partofcosmos-site/pocket-companion/assets/cdn_audit/01_system_architecture_block_diagram.png

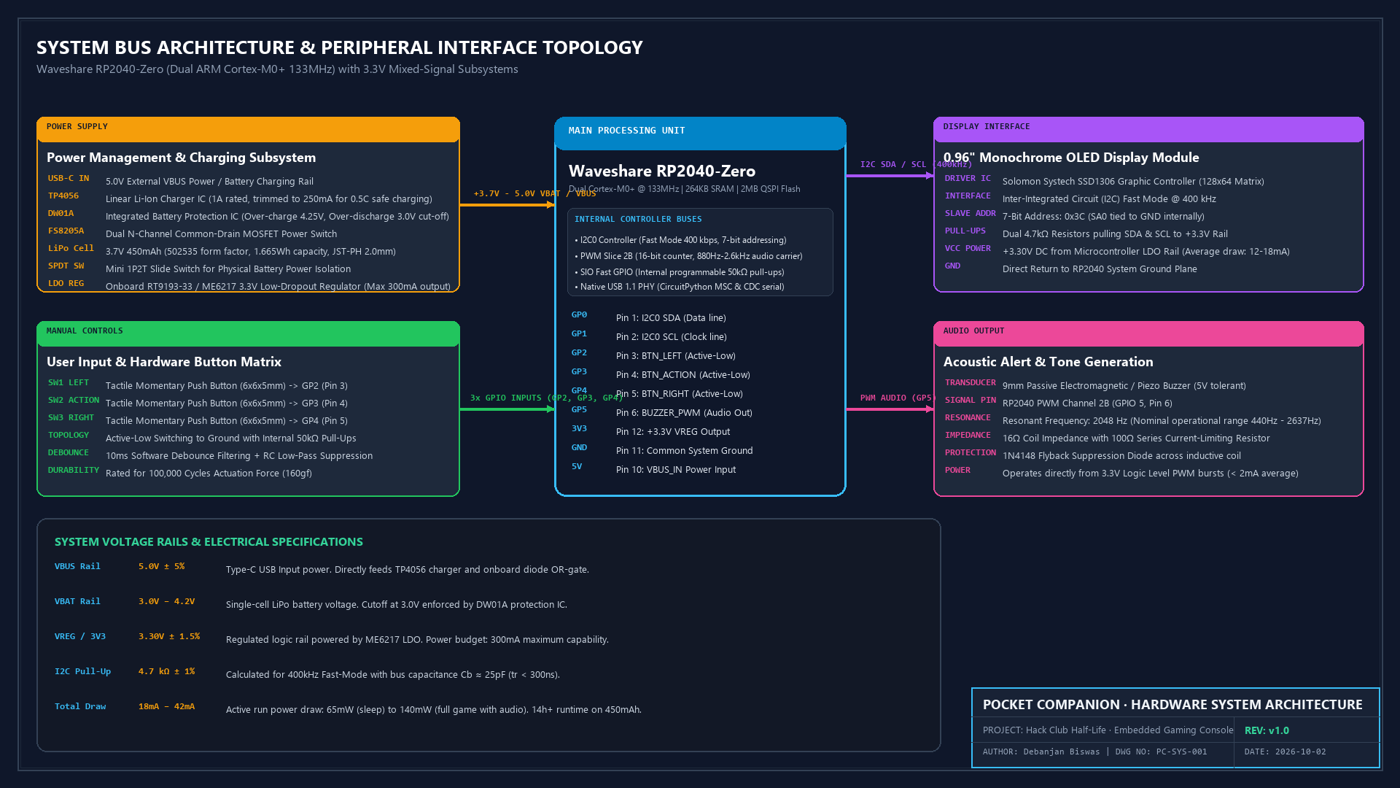
assets/cdn_audit/01_system_architecture_block_diagram.png
