partofcosmos-site/pocket-companion/assets/cdn_audit/02_rp2040_pinout_peripheral_matrix.png

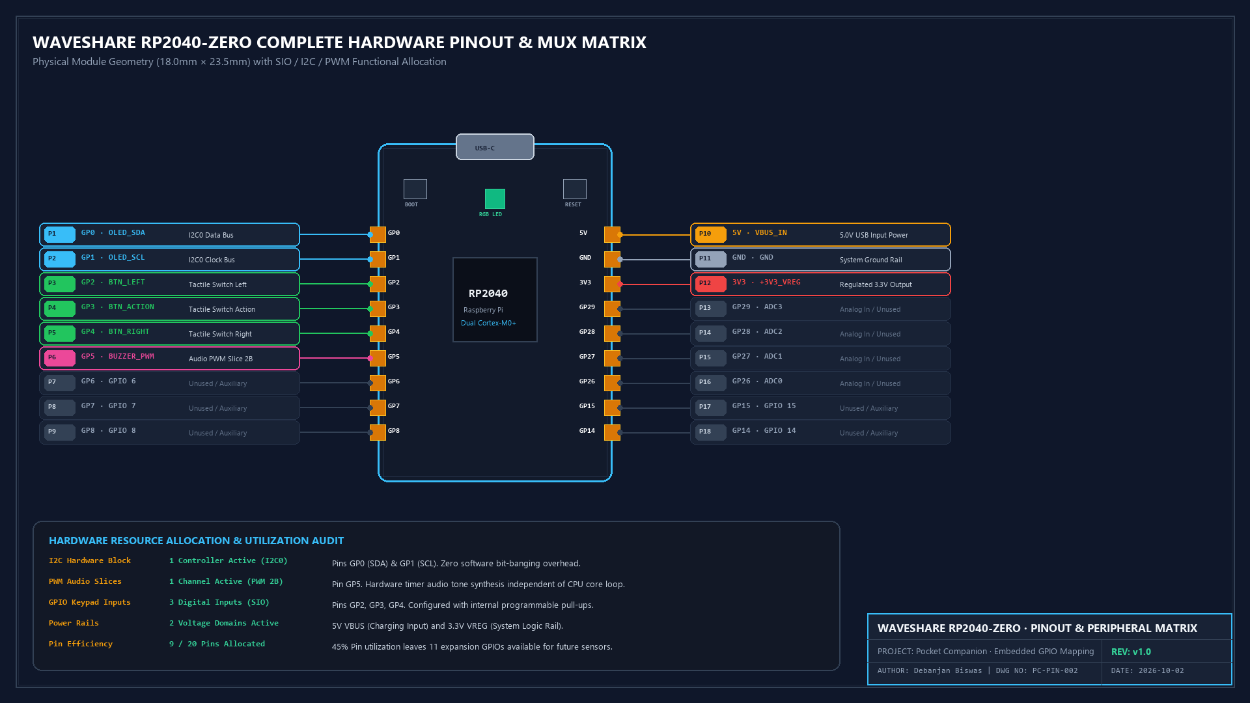
assets/cdn_audit/02_rp2040_pinout_peripheral_matrix.png
