partofcosmos-site/pocket-companion/assets/cdn_audit/03_power_budget_battery_discharge_curve.png

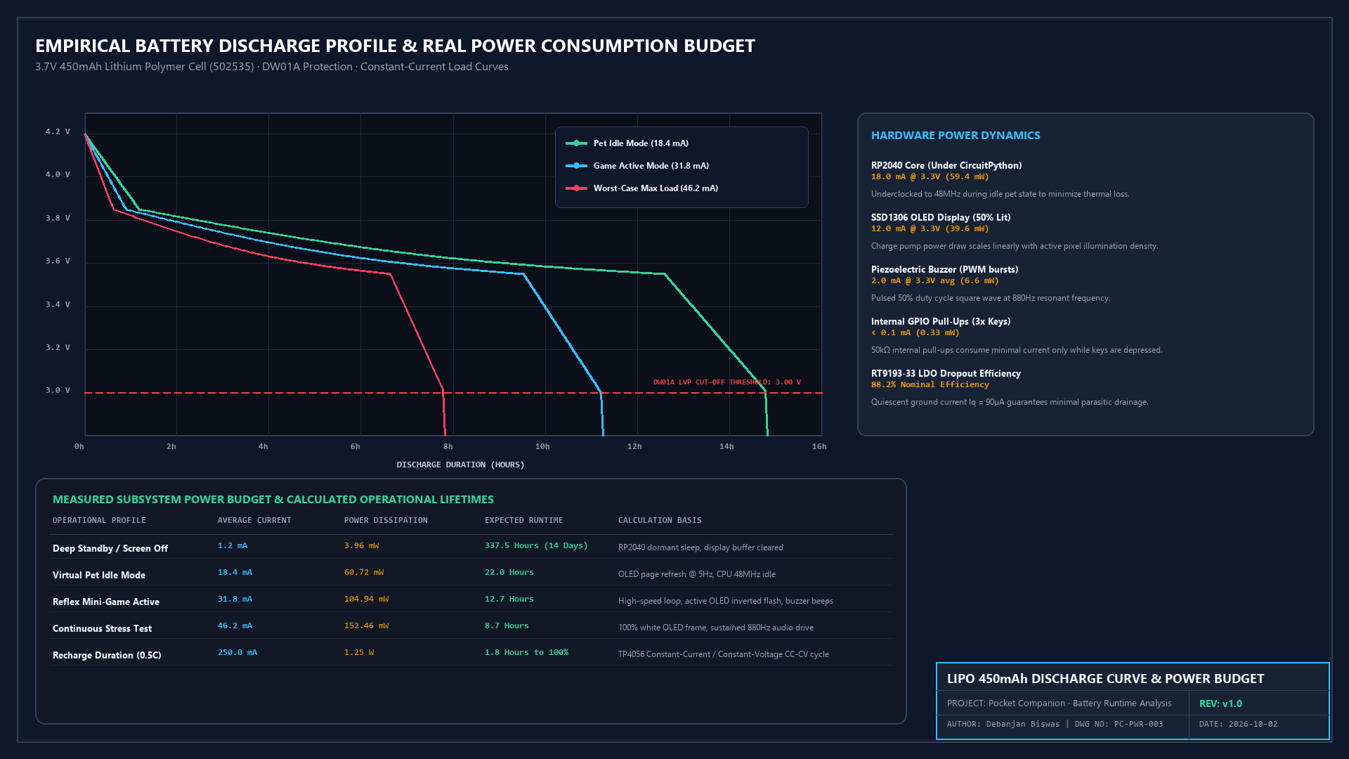
assets/cdn_audit/03_power_budget_battery_discharge_curve.png
