partofcosmos-site/pocket-companion/assets/cdn_audit/05_easyeda_schematic_capture.png

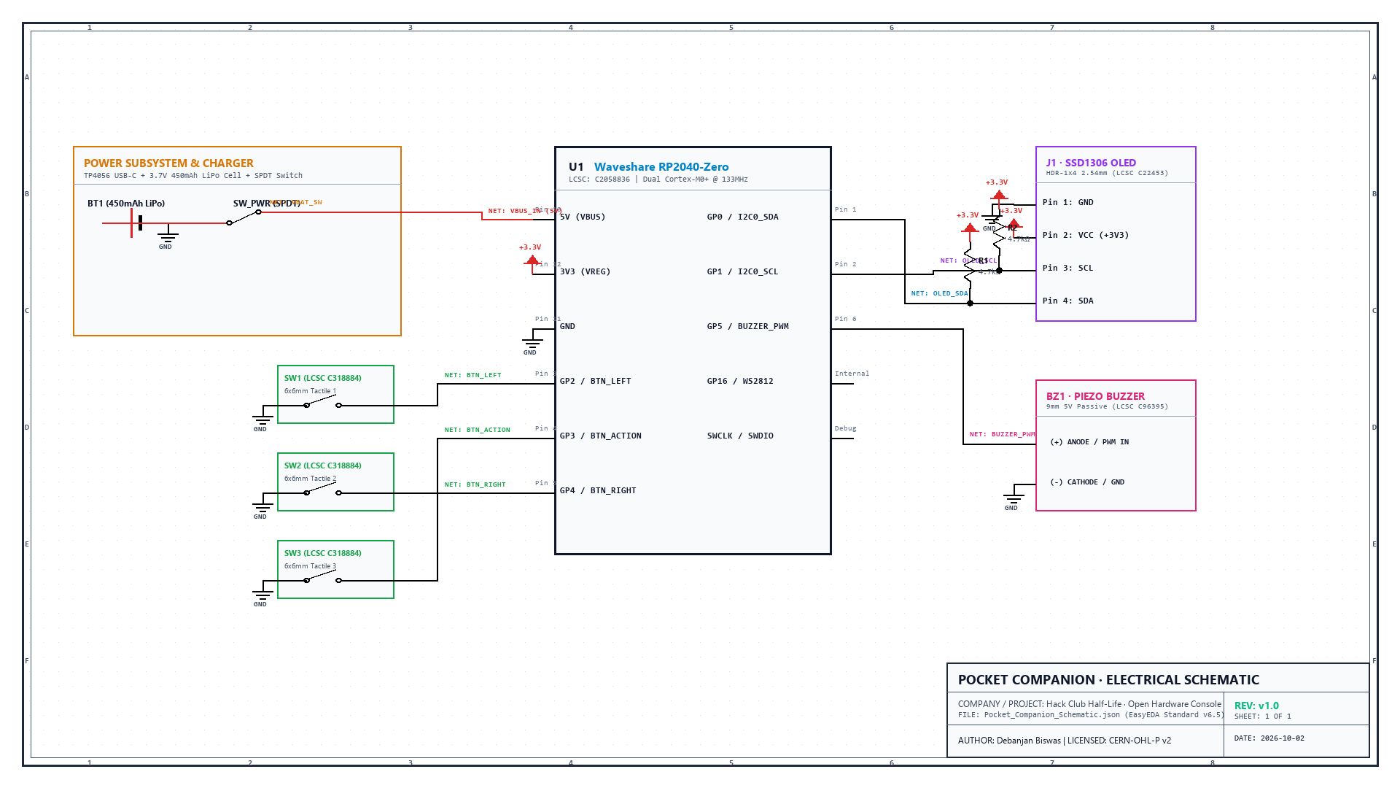
assets/cdn_audit/05_easyeda_schematic_capture.png
