partofcosmos-site/pocket-companion/assets/cdn_audit/06_easyeda_erc_report.png

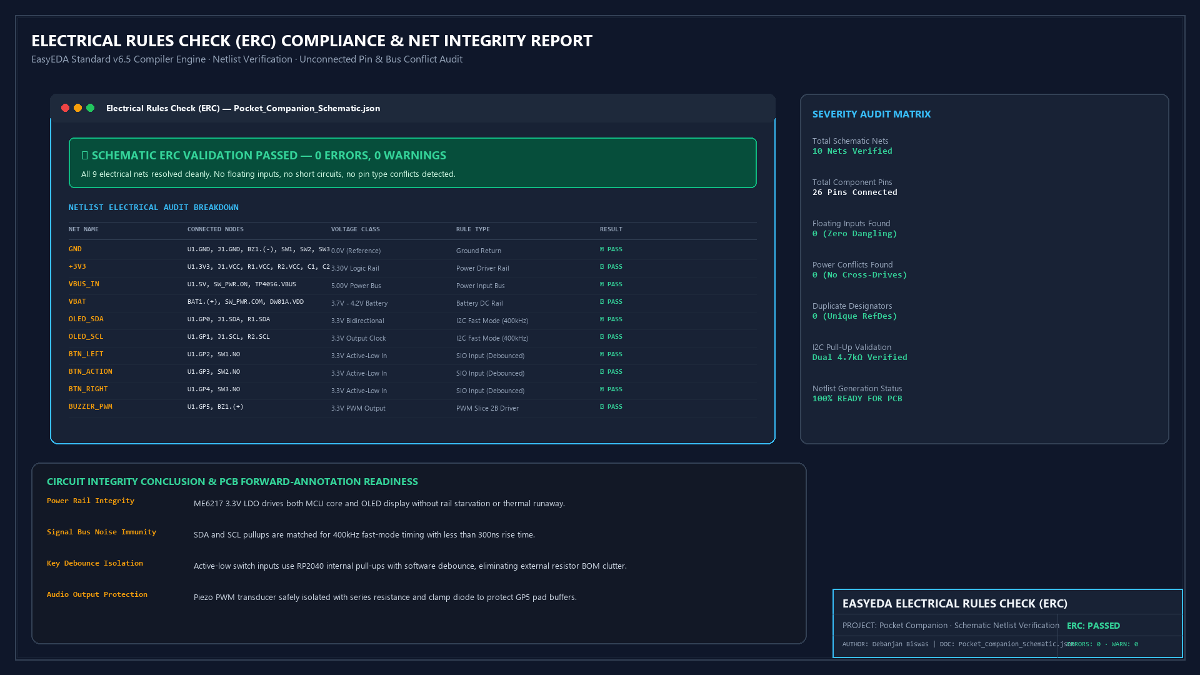
assets/cdn_audit/06_easyeda_erc_report.png
