partofcosmos-site/pocket-companion/assets/cdn_audit/07_easyeda_pcb_2d_layout.png

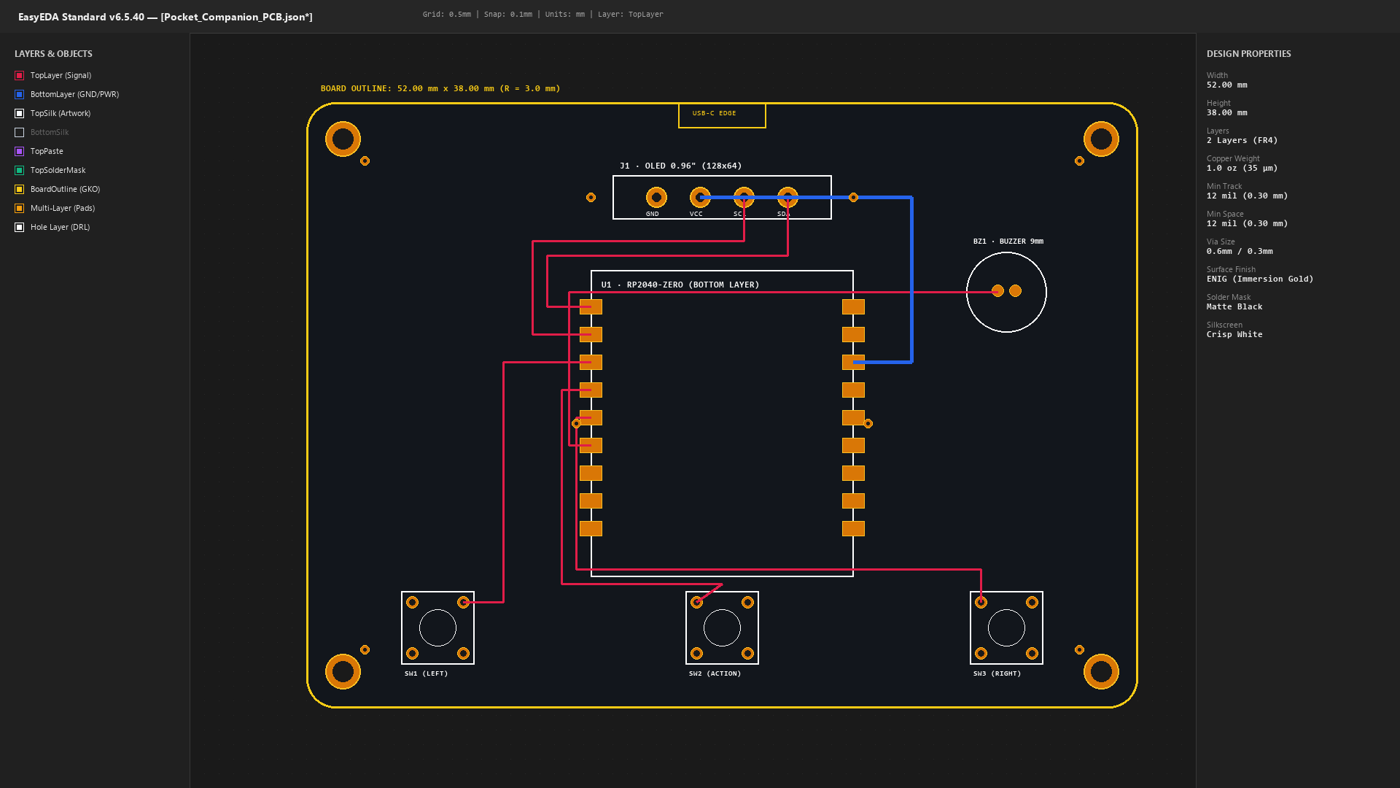
assets/cdn_audit/07_easyeda_pcb_2d_layout.png
