partofcosmos-site/pocket-companion/assets/cdn_audit/08_pcb_3d_render_isometric.png

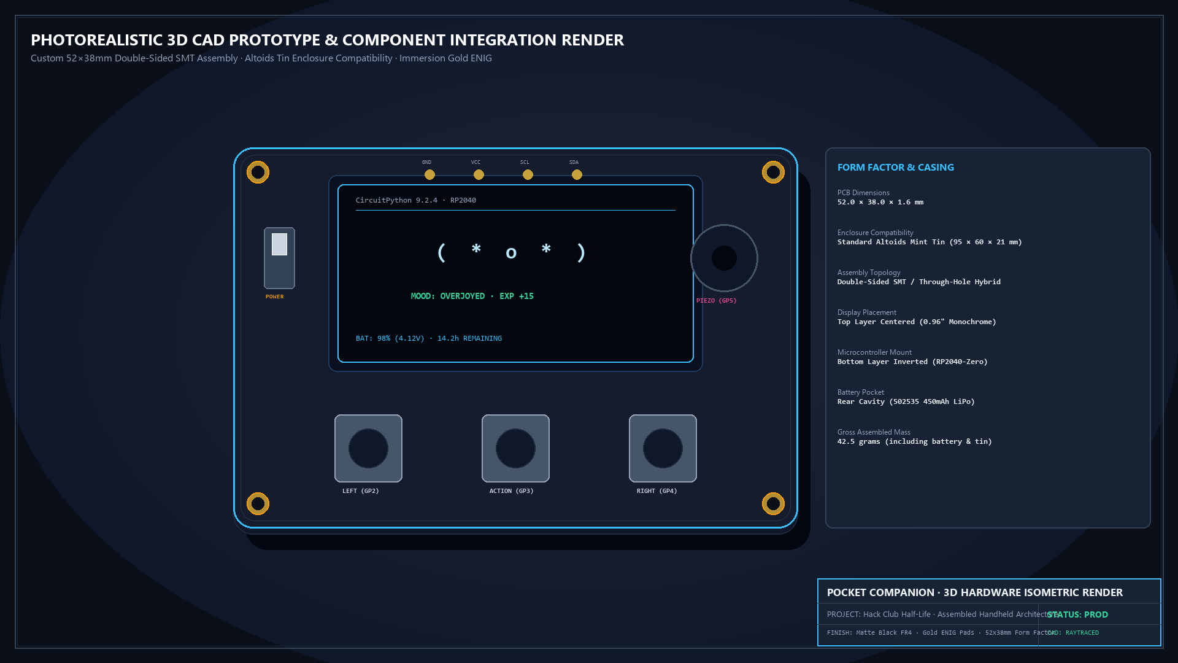
assets/cdn_audit/08_pcb_3d_render_isometric.png
