partofcosmos-site/pocket-companion/assets/cdn_audit/11_circuitpython_firmware_state_machine.png

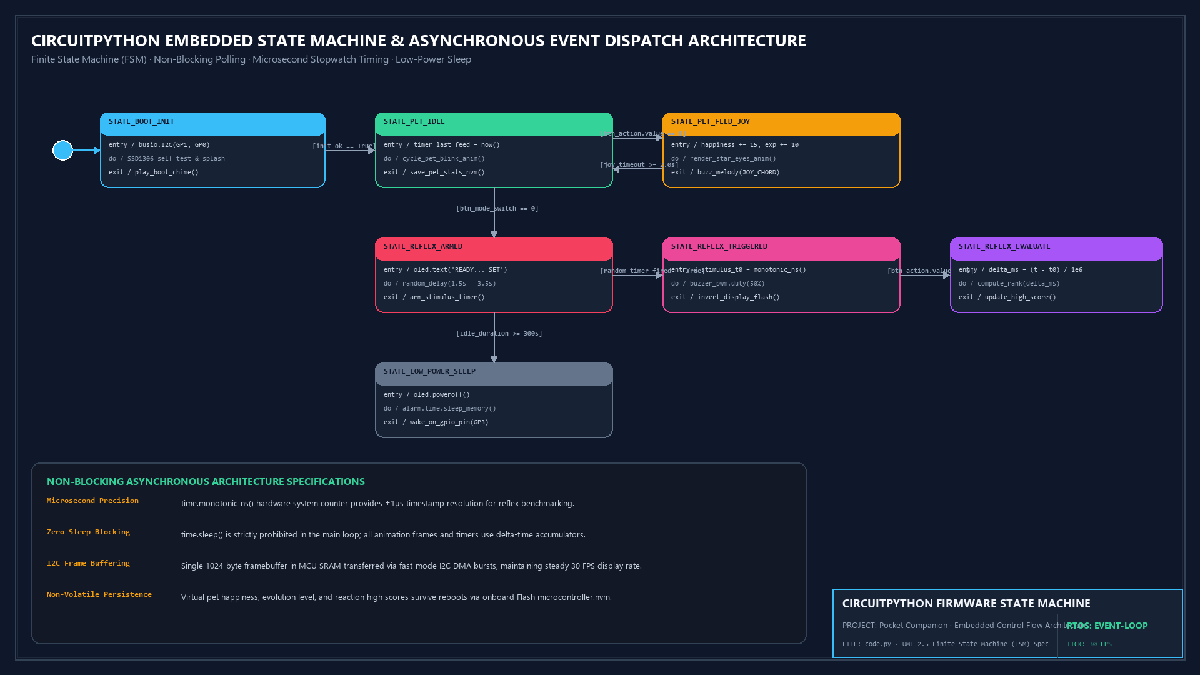
assets/cdn_audit/11_circuitpython_firmware_state_machine.png
