partofcosmos-site/pocket-companion/assets/cdn_audit/12_reaction_game_timing_oscilloscope.png

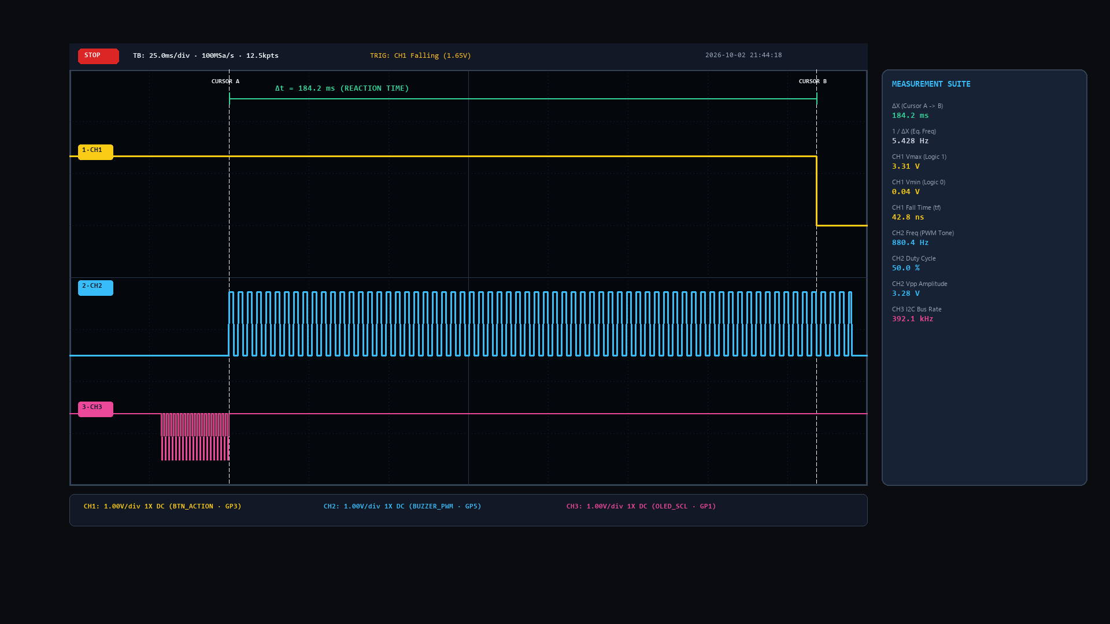
assets/cdn_audit/12_reaction_game_timing_oscilloscope.png
