partofcosmos-site/pocket-companion/assets/cutaway_section.png

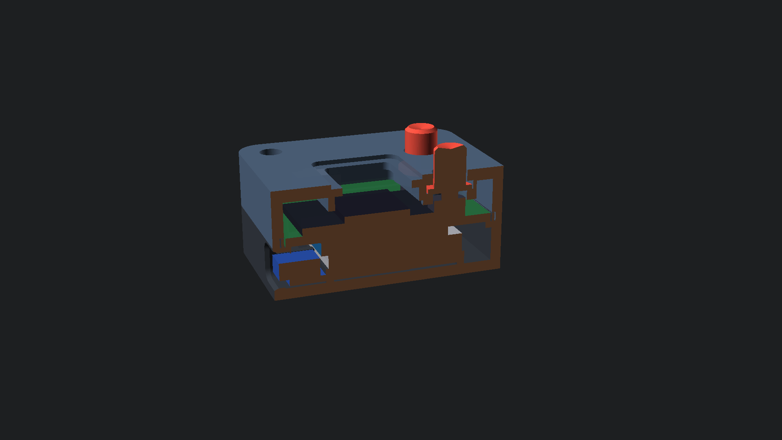
assets/cutaway_section.png
