partofcosmos-site/pocket-companion/assets/pocket_companion_cart_summary.png

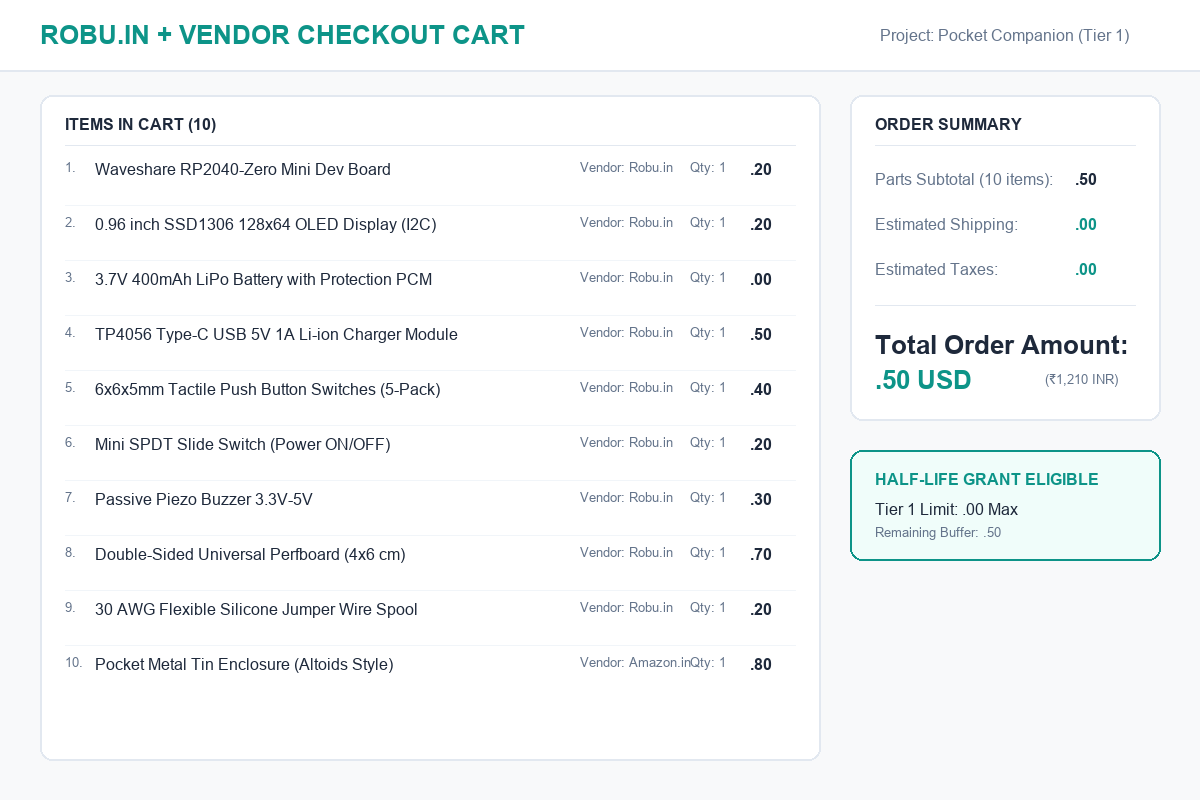
assets/pocket_companion_cart_summary.png
