partofcosmos-site/pocket-companion/assets/portal_live_state.png

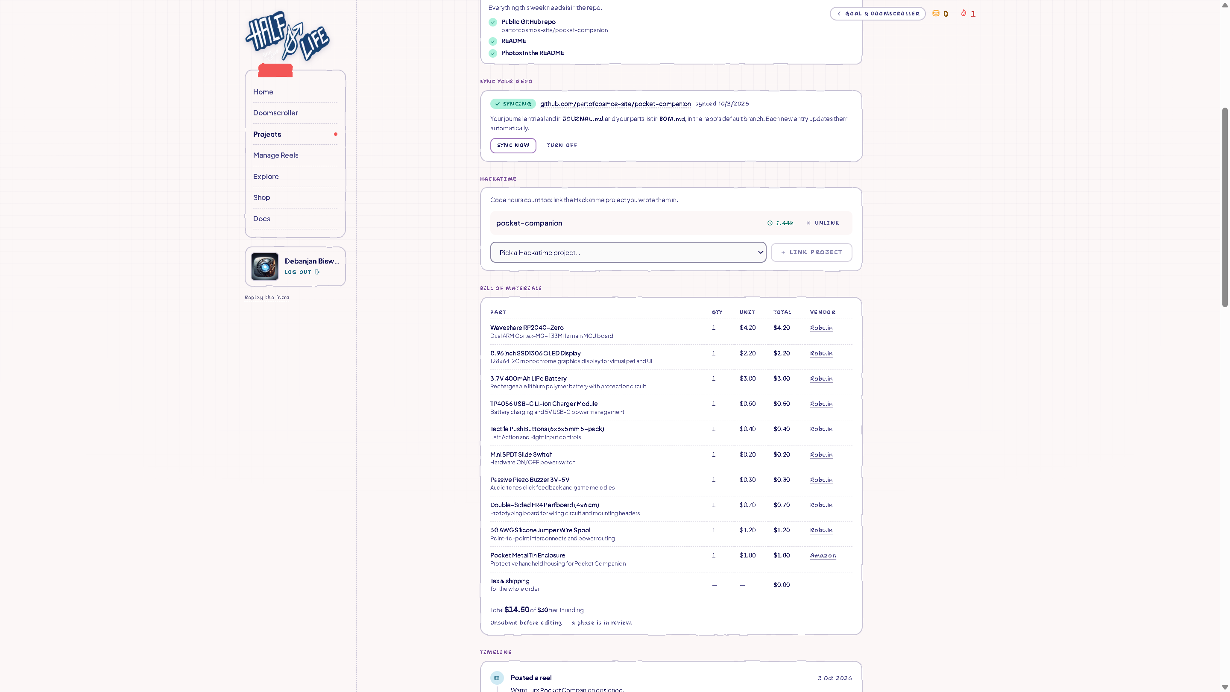
assets/portal_live_state.png
