partofcosmos-site/pocket-companion/assets/reels/poster_scene3_hardware_teardown.jpg

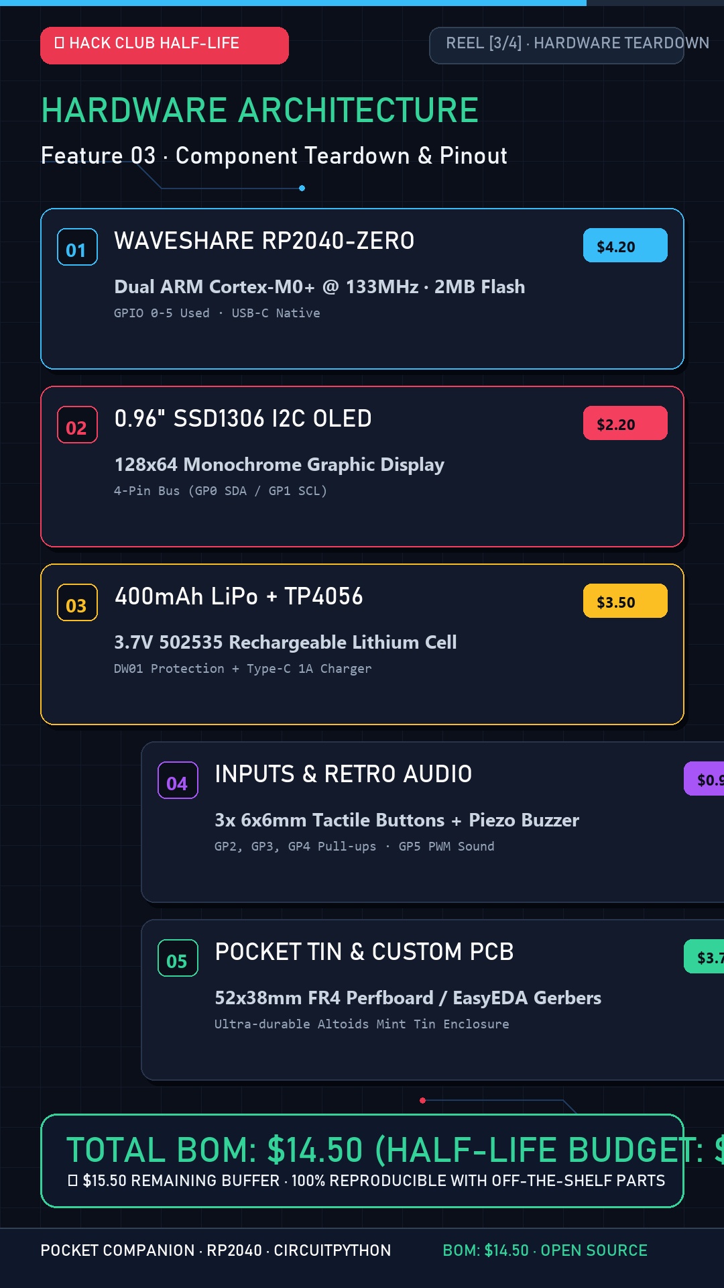
assets/reels/poster_scene3_hardware_teardown.jpg
