partofcosmos-site/pocket-companion/assets/submission_confirmed.png

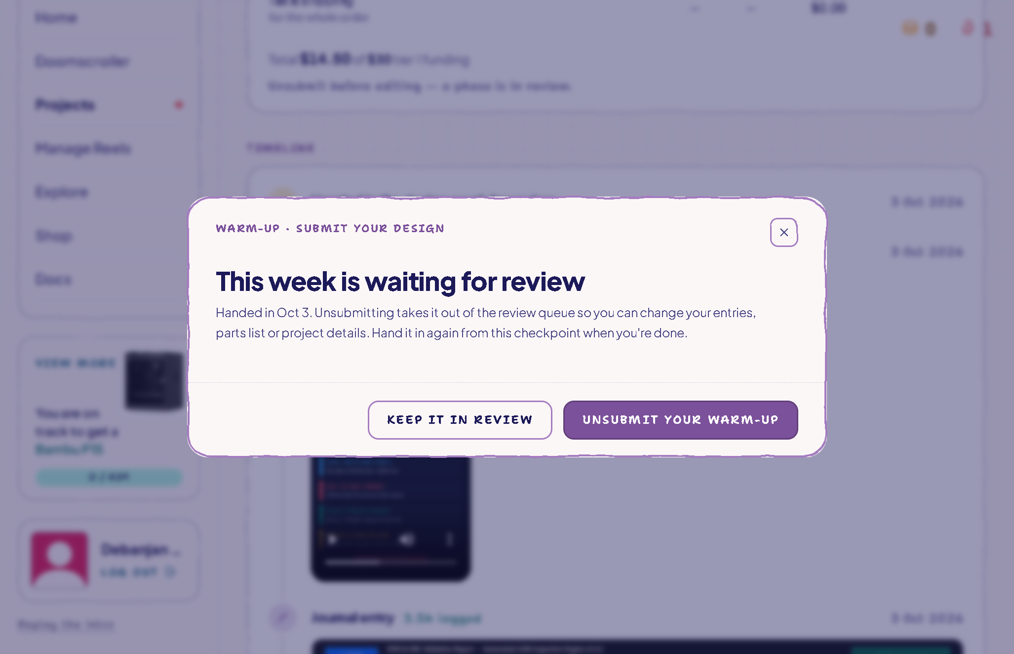
assets/submission_confirmed.png
