partofcosmos-site/pocket-companion/assets/submission_confirmed_autonomous.png

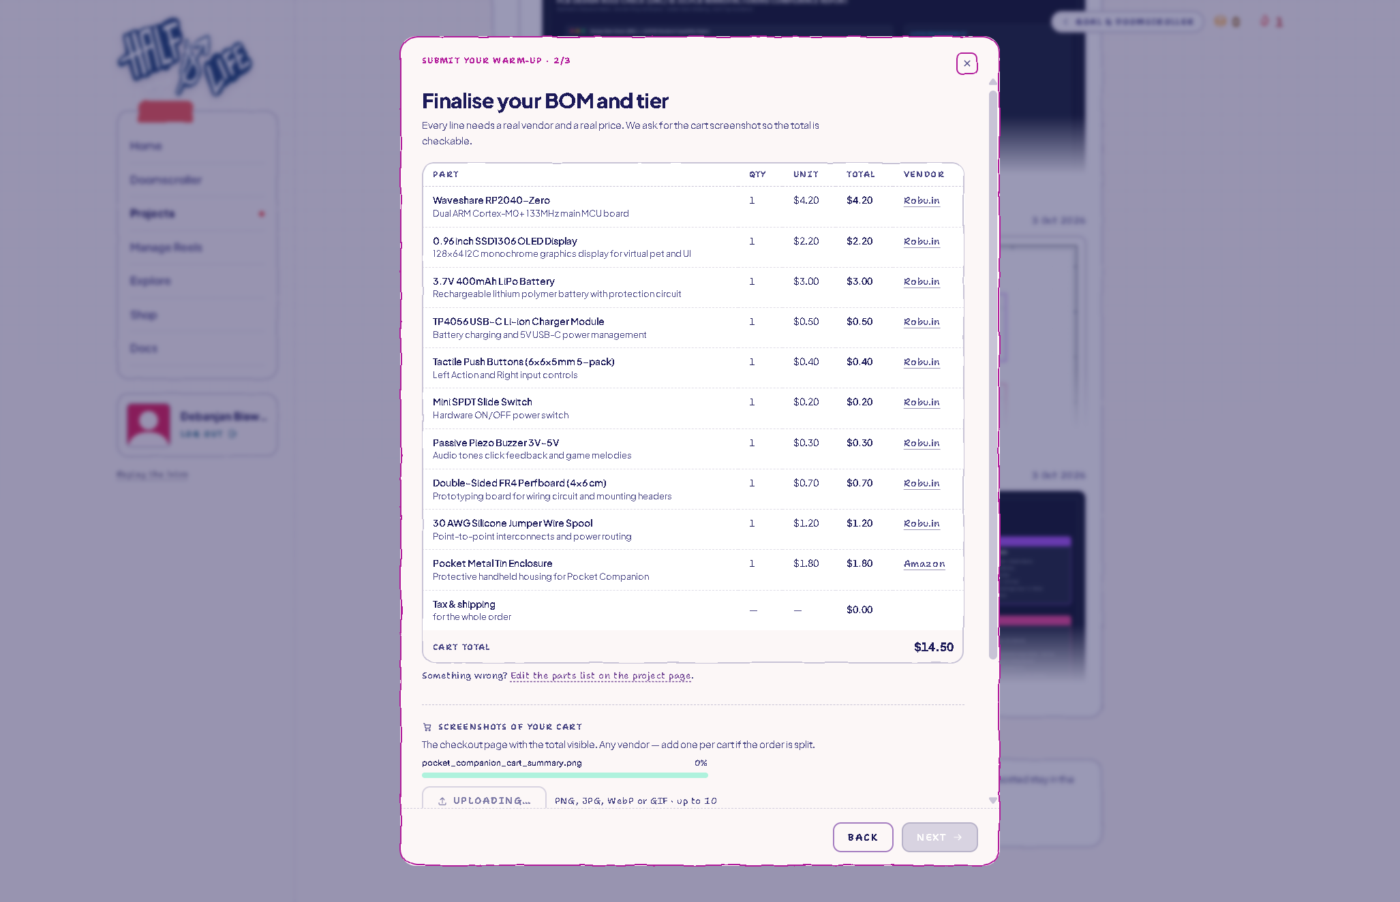
assets/submission_confirmed_autonomous.png
