partofcosmos-site/pocket-companion/assets/submission_confirmed_final.png

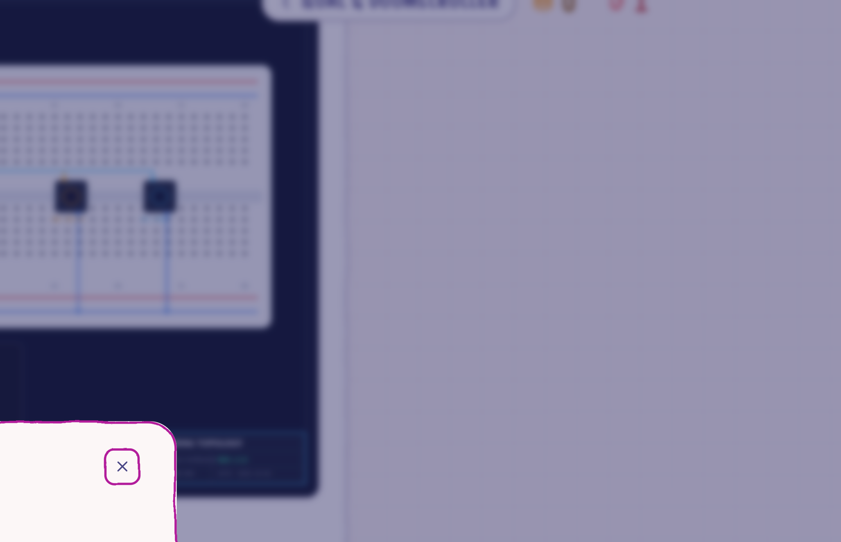
assets/submission_confirmed_final.png
