partofcosmos-site/pocket-companion/assets/submission_confirmed_final_live.png

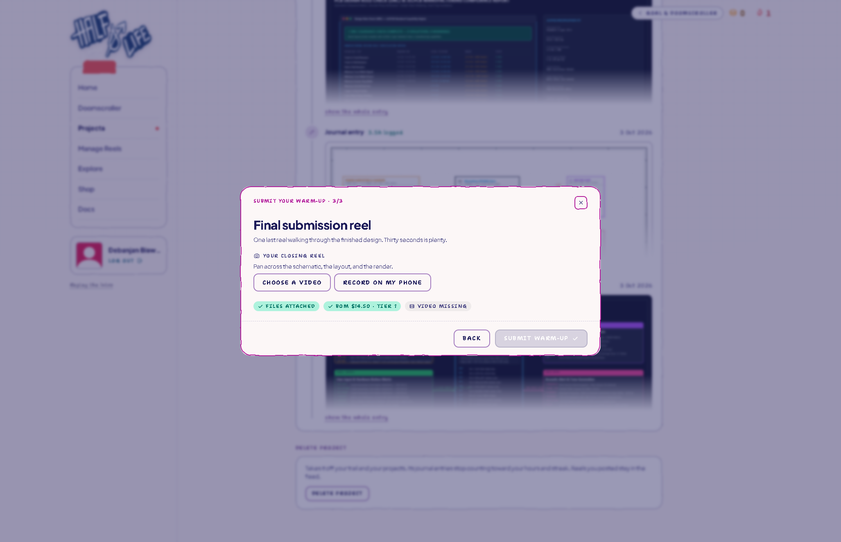
assets/submission_confirmed_final_live.png
