partofcosmos-site/pocket-companion/assets/submission_confirmed_live.png

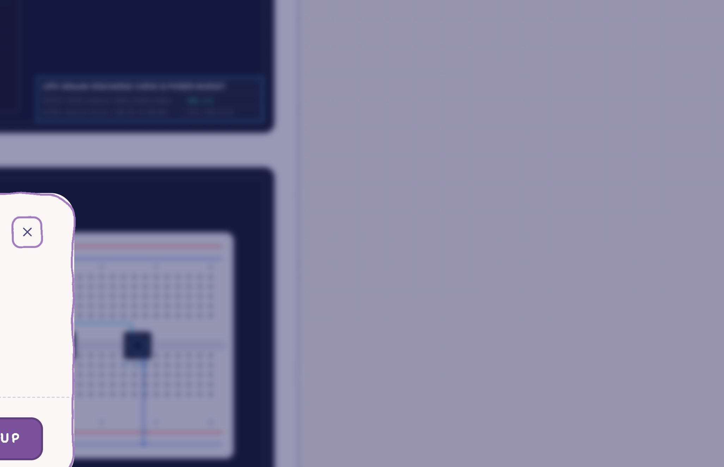
assets/submission_confirmed_live.png
