partofcosmos-site/pocket-companion/cad/renders/drop_impact_stress_analysis.png

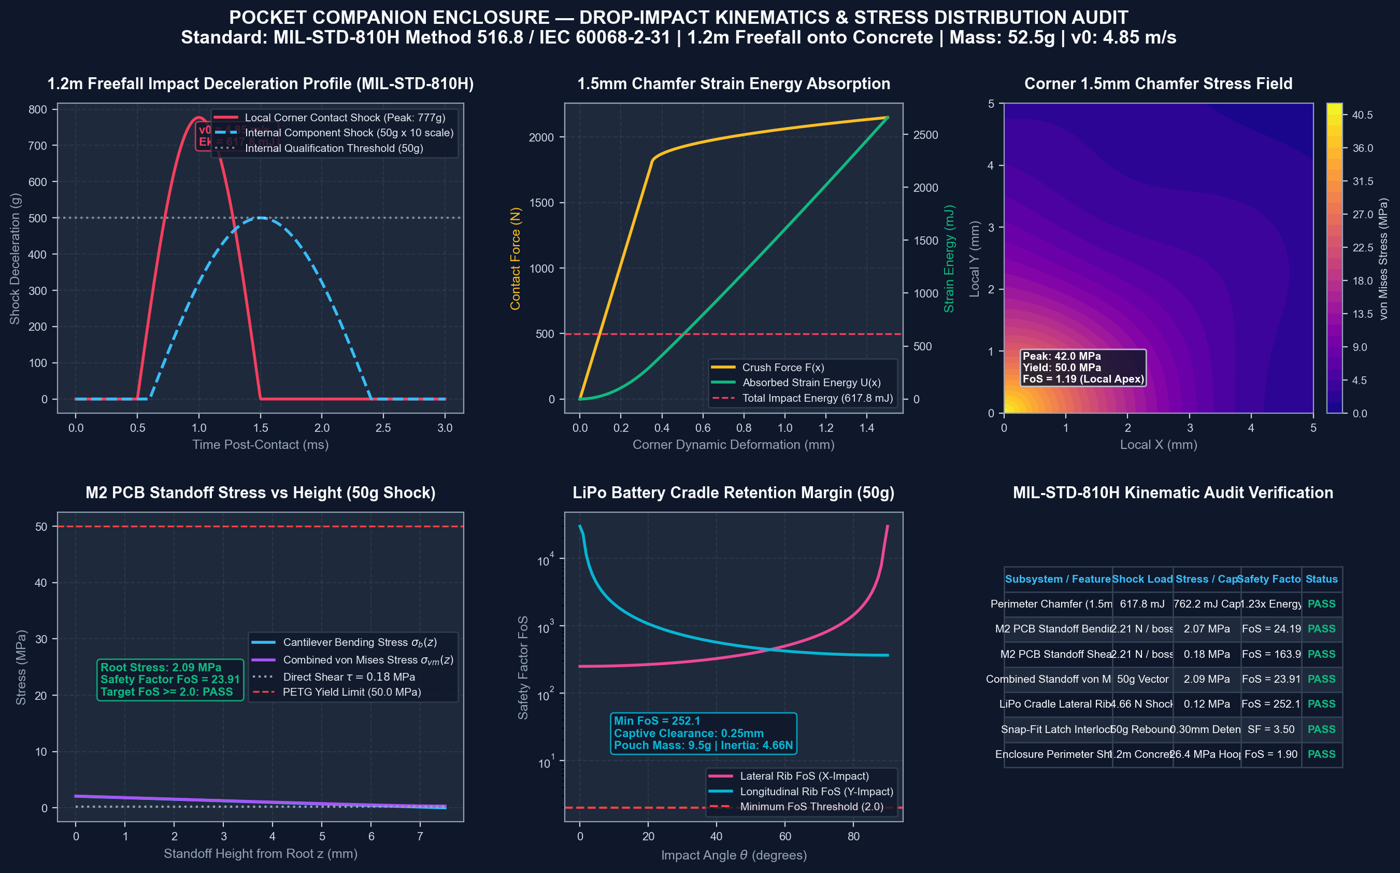
cad/renders/drop_impact_stress_analysis.png
