partofcosmos-site/pocket-companion/cad/renders/ortho_front.png

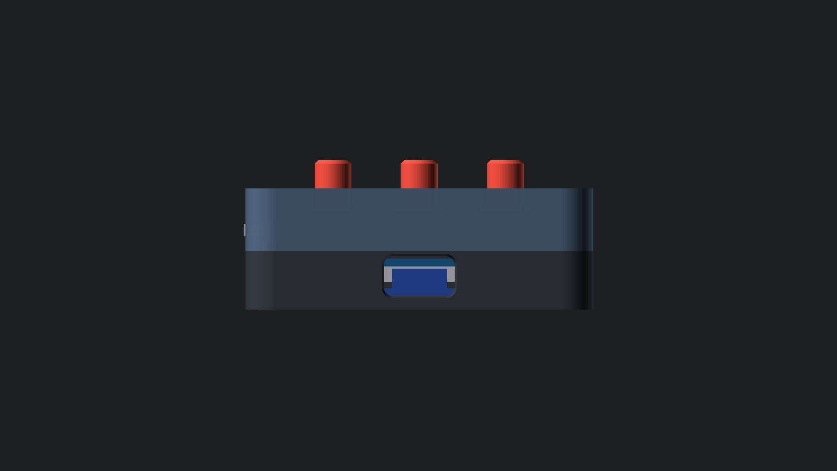
cad/renders/ortho_front.png
