partofcosmos-site/pocket-companion/cad/renders/ortho_side.png

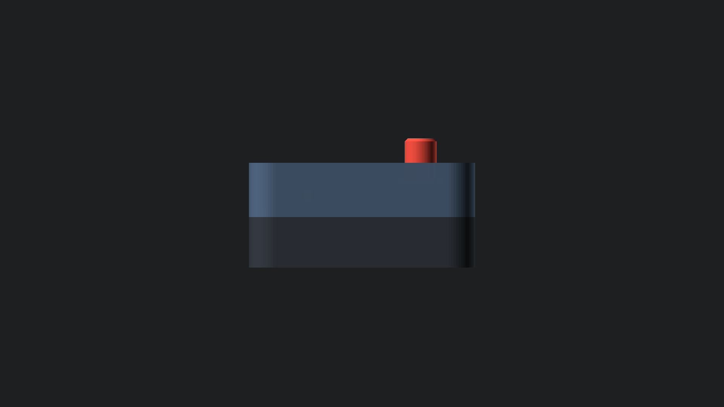
cad/renders/ortho_side.png
