partofcosmos-site/pocket-companion/cad/renders/ortho_top.png

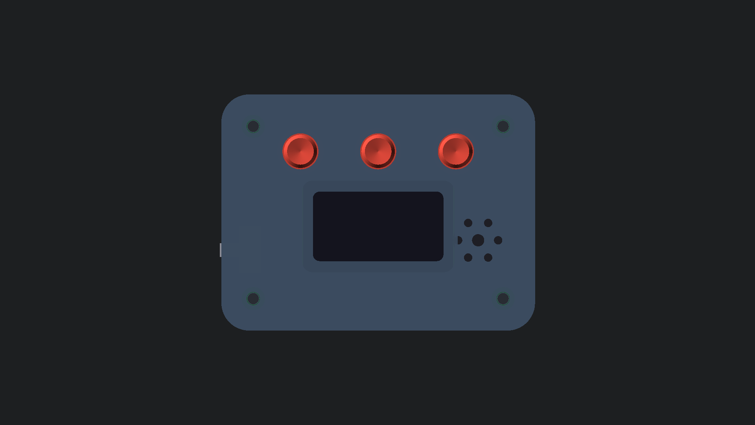
cad/renders/ortho_top.png
