partofcosmos-site/pocket-companion/cad/renders/thermal_tolerance_stackup.png

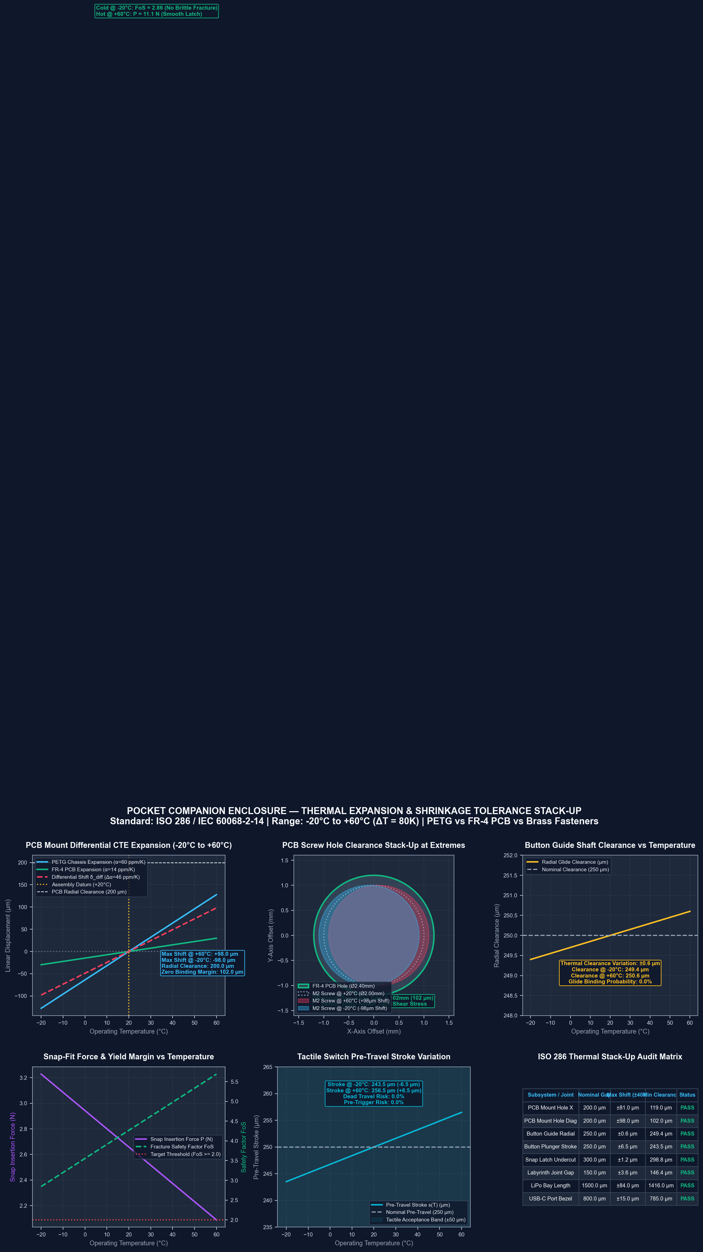
cad/renders/thermal_tolerance_stackup.png
