partofcosmos-site/pocket-companion/hardware/gerbers/rendered_layers/board_outline_gko.png

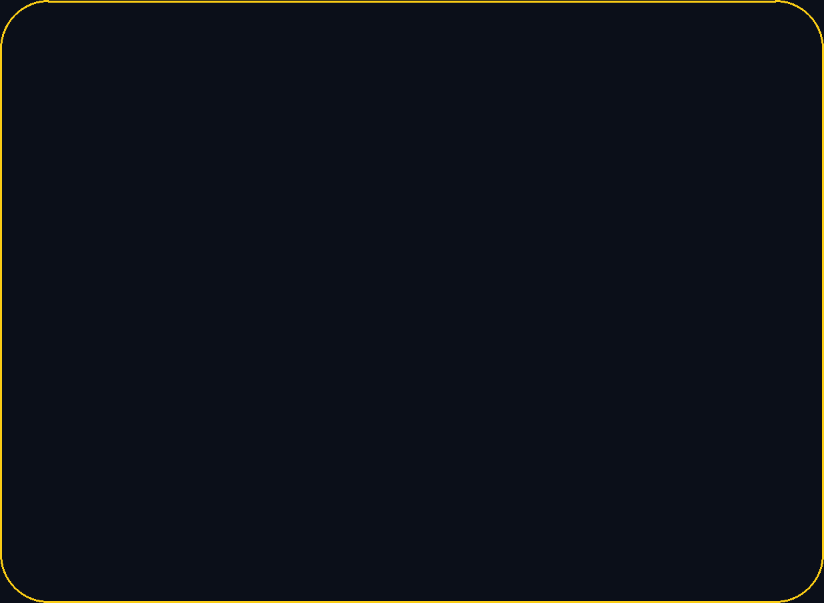
hardware/gerbers/rendered_layers/board_outline_gko.png
