partofcosmos-site/pocket-companion/hardware/gerbers/rendered_layers/bottom_copper_gbl.png

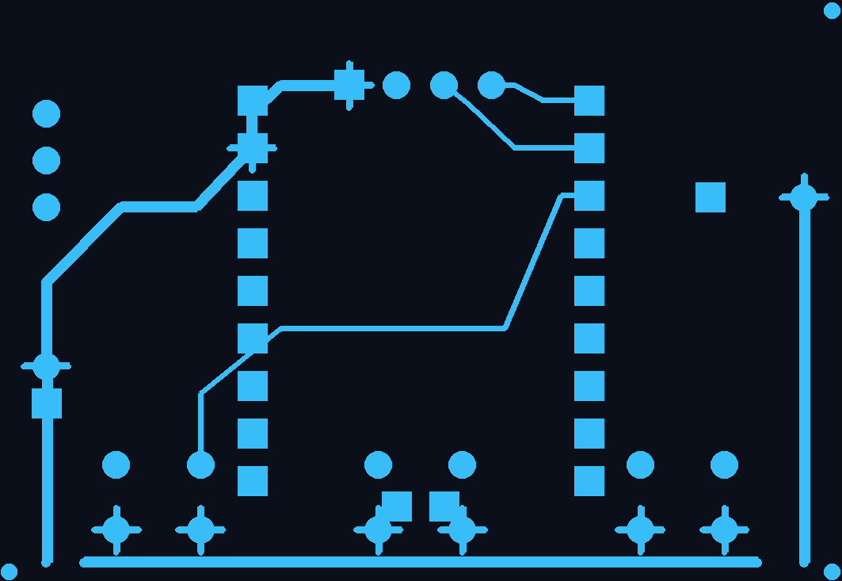
hardware/gerbers/rendered_layers/bottom_copper_gbl.png
