partofcosmos-site/pocket-companion/hardware/gerbers/rendered_layers/bottom_silkscreen_gbo.png

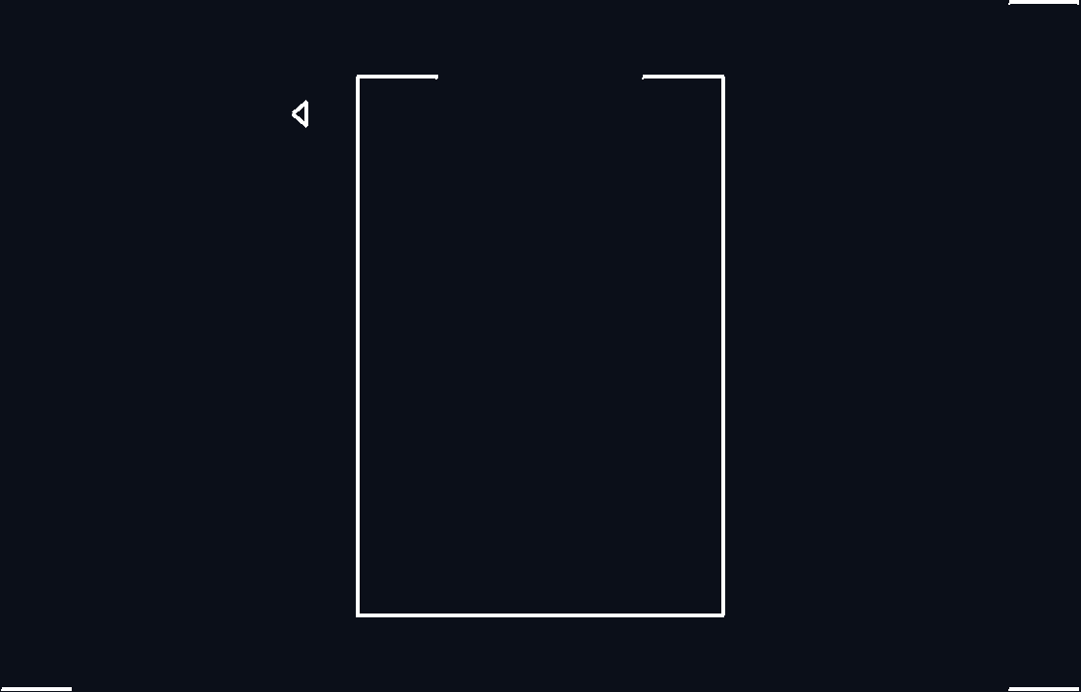
hardware/gerbers/rendered_layers/bottom_silkscreen_gbo.png
