partofcosmos-site/pocket-companion/hardware/gerbers/rendered_layers/composite_v2_xray.png

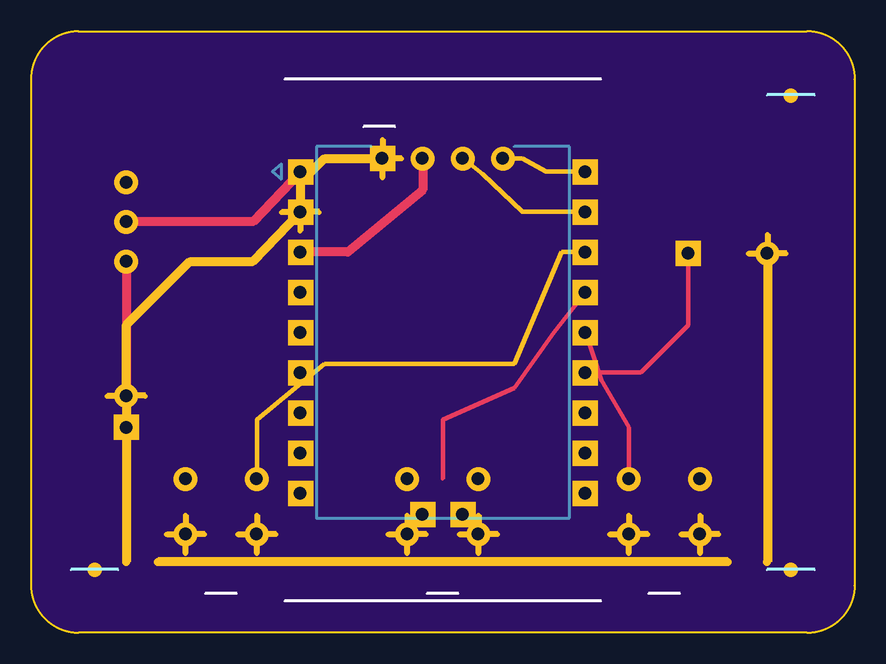
hardware/gerbers/rendered_layers/composite_v2_xray.png
