partofcosmos-site/pocket-companion/hardware/gerbers/rendered_layers/drill_holes_drl.png

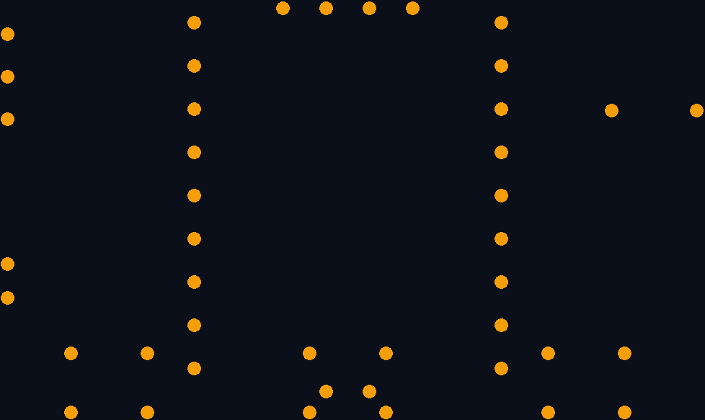
hardware/gerbers/rendered_layers/drill_holes_drl.png
