partofcosmos-site/pocket-companion/hardware/gerbers/rendered_layers/top_copper_gtl.png

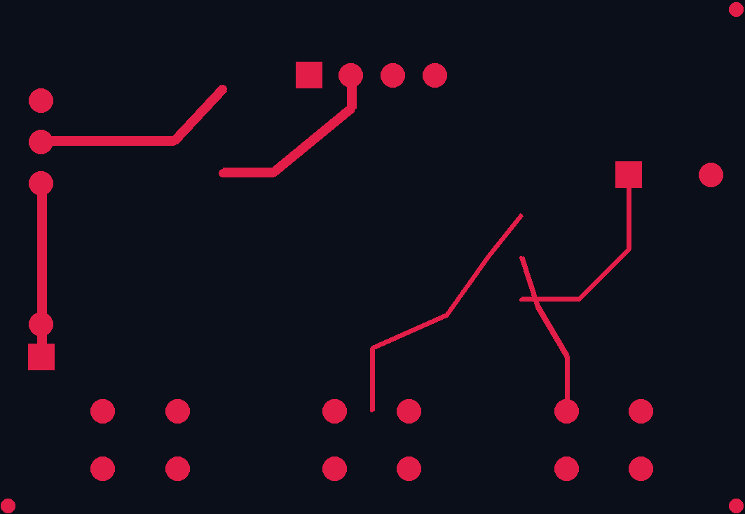
hardware/gerbers/rendered_layers/top_copper_gtl.png
