partofcosmos-site/pocket-companion/hardware/gerbers/rendered_layers/top_silkscreen_gto.png

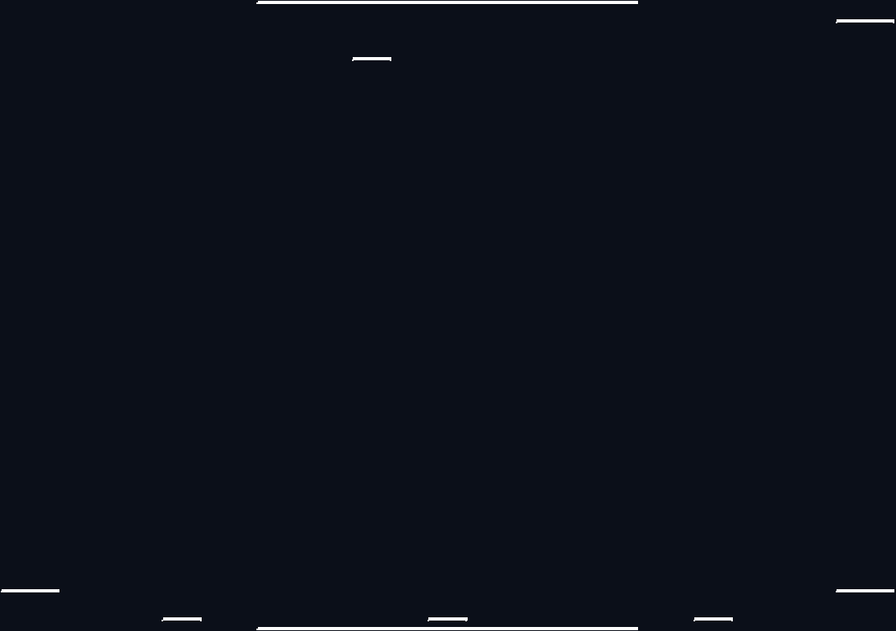
hardware/gerbers/rendered_layers/top_silkscreen_gto.png
