partofcosmos-site/pocket-companion/hardware/rp2040_size.jpg

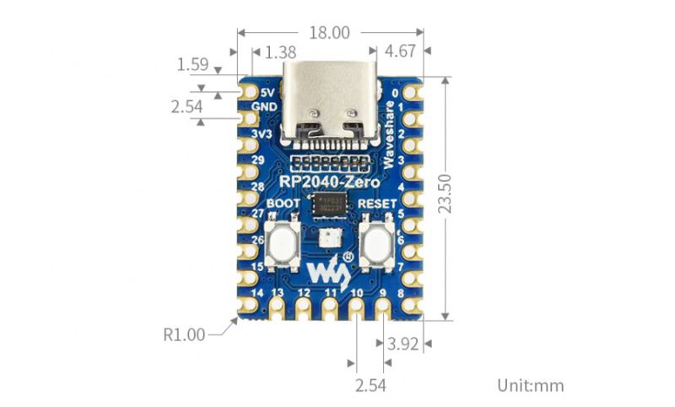
hardware/rp2040_size.jpg
