partofcosmos-site/pocket-companion/assets/cdn_audit/10_gerber_manufacturing_stackup_preview.png

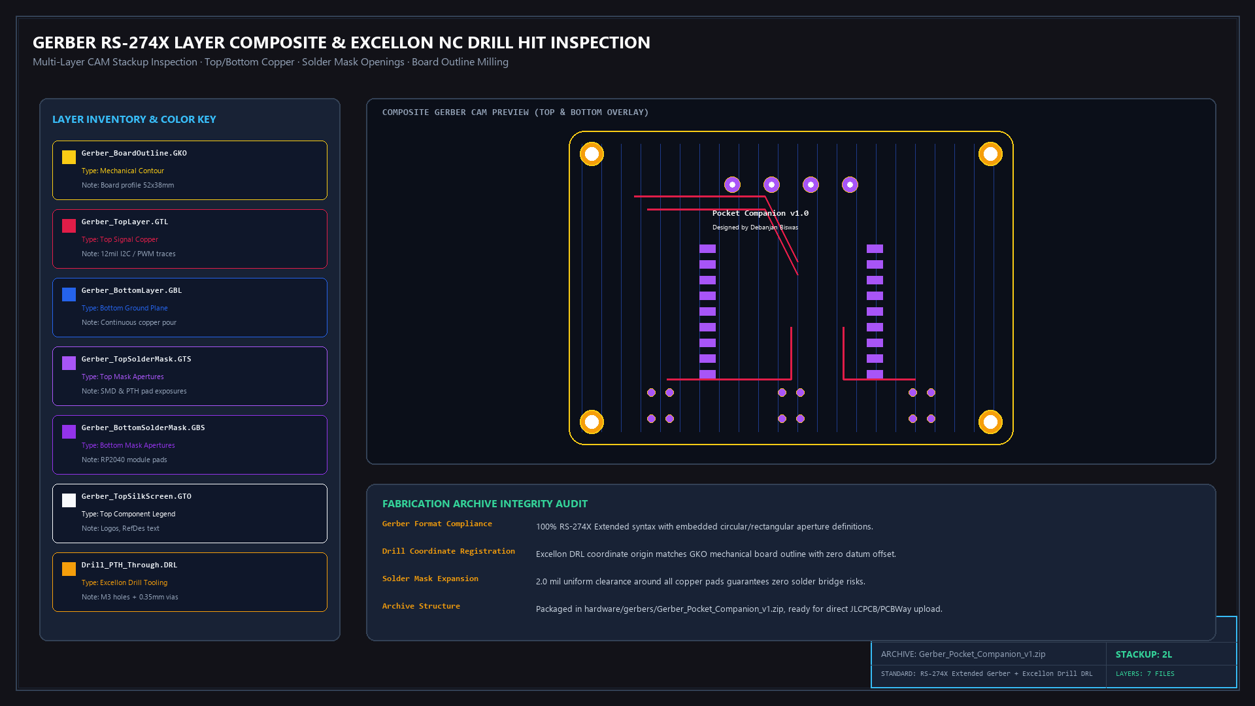
assets/cdn_audit/10_gerber_manufacturing_stackup_preview.png
