partofcosmos-site/pocket-companion/hardware/gerbers/rendered_layers/bottom_soldermask_gbs.png

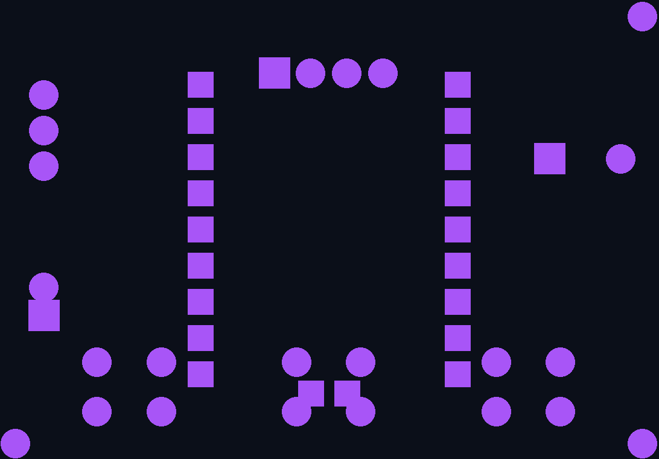
hardware/gerbers/rendered_layers/bottom_soldermask_gbs.png
