partofcosmos-site/pocket-companion/hardware/gerbers/rendered_layers/top_soldermask_gts.png

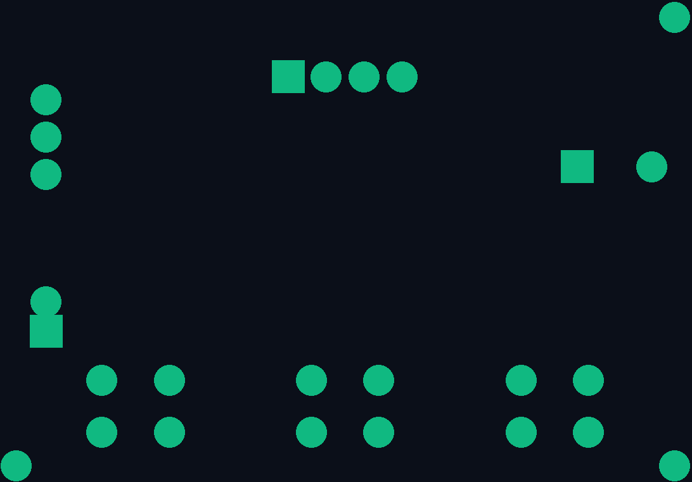
hardware/gerbers/rendered_layers/top_soldermask_gts.png
