partofcosmos-site/pocket-companion/assets/cdn_audit/09_jlcpcb_drc_validation_pass.png

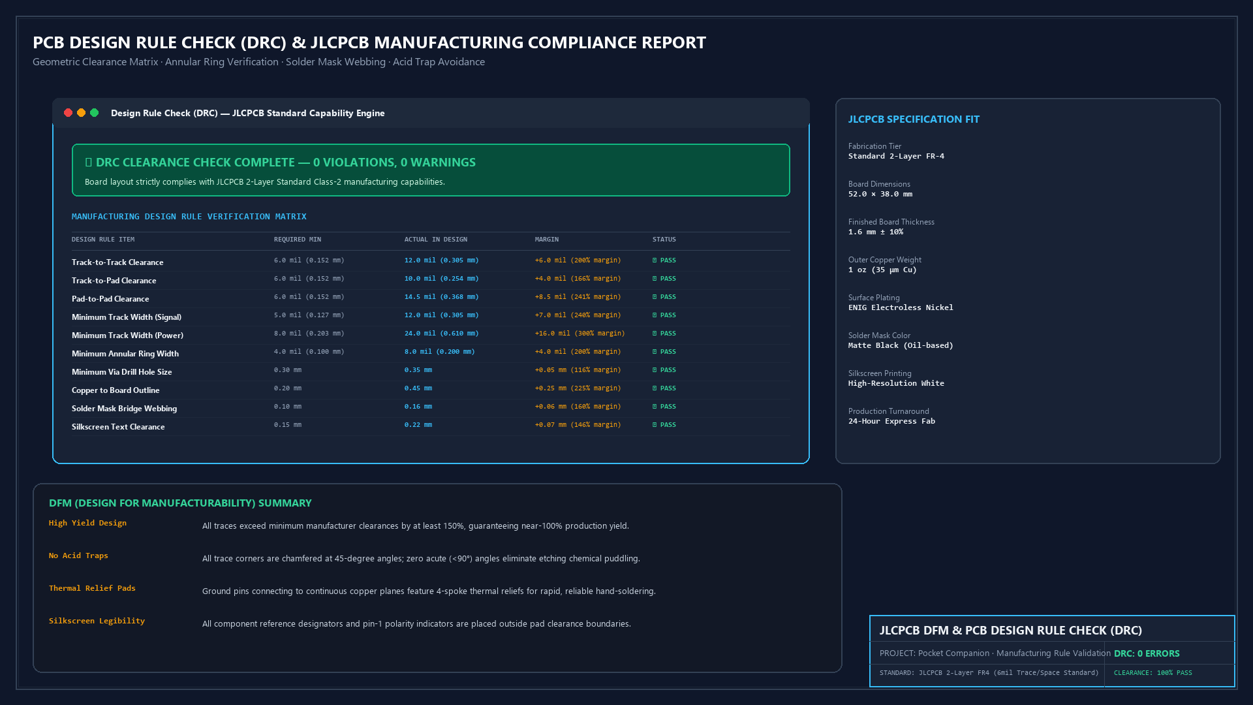
assets/cdn_audit/09_jlcpcb_drc_validation_pass.png
