partofcosmos-site/pocket-companion/hardware/gerbers/rendered_layers/all_layers_test.png

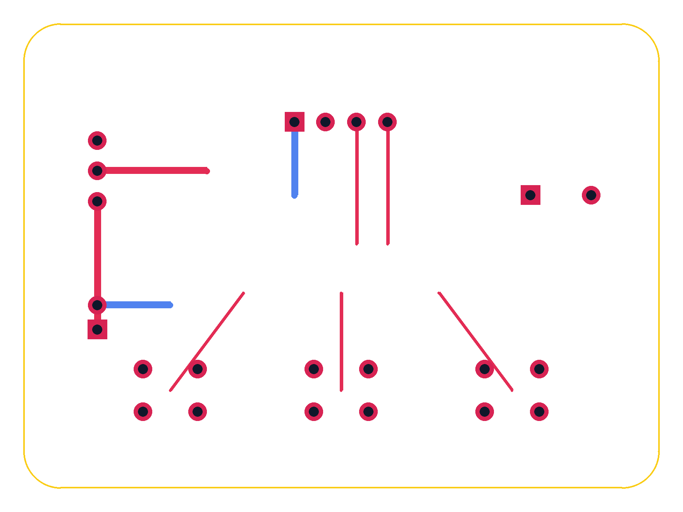
hardware/gerbers/rendered_layers/all_layers_test.png
