partofcosmos-site/pocket-companion/hardware/gerbers/rendered_layers/composite_test.png

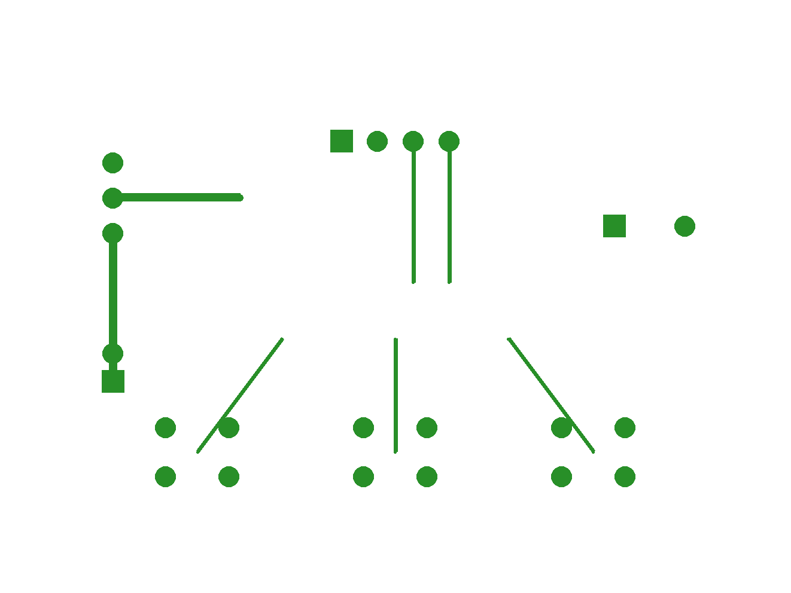
hardware/gerbers/rendered_layers/composite_test.png
