partofcosmos-site/pocket-companion/hardware/gerbers/rendered_layers/realistic_pcb_test.png

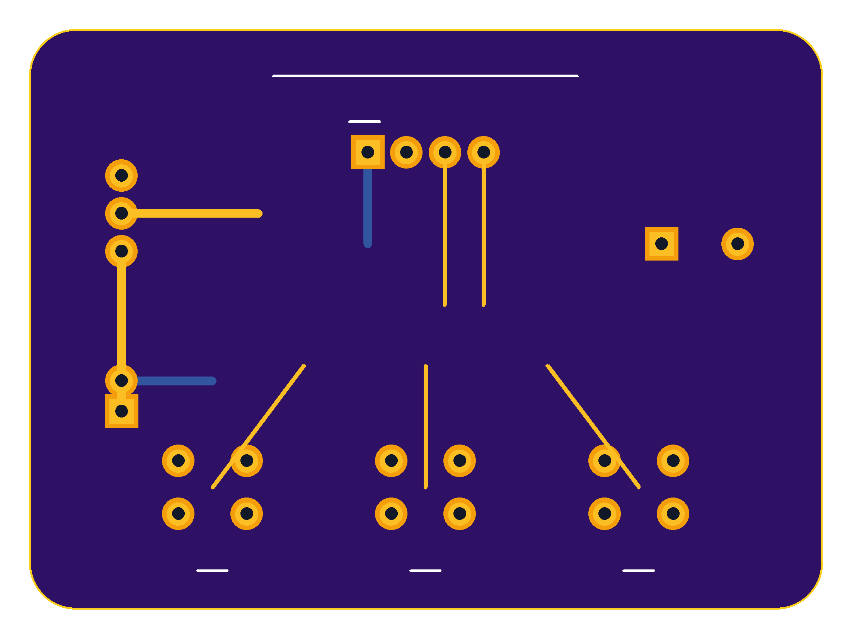
hardware/gerbers/rendered_layers/realistic_pcb_test.png
