partofcosmos-site/pocket-companion/portal_sentry_daemon.py

import asyncio
import base64
import datetime
import json
import os
import sys
import time
import urllib.request
import websockets

if sys.stdout.encoding != 'utf-8':
    sys.stdout.reconfigure(encoding='utf-8')

CDP_JSON_URL = 'http://127.0.0.1:9100/json'
PROJECT_ID = 'cmuqw217z02uz01rlatu9wyrg'
HEARTBEAT_FILE = r'C:\Users\white\pocket-companion\sentry_heartbeat.json'
LOG_FILE = r'C:\Users\white\pocket-companion\sentry_status.log'
SCREENSHOT_FILE = r'C:\Users\white\pocket-companion\assets\portal_live_state.png'

CDN_IMAGE_URLS = [
    "https://halflife.hackclub-assets.com/hackclub-half-life/covers/gSMICPeKfFIX4r61sX8jLHHguUkM0Btr/5e449e176c85c1d4a4318d1d9541141d42ec89aa26c34e6a881e93d6927da231.png",
    "https://halflife.hackclub-assets.com/hackclub-half-life/sessions/gSMICPeKfFIX4r61sX8jLHHguUkM0Btr/71f1e30cb4aaa1d3645ea29fa7da0e0f4d5774497b45c4ee4927fcc0c868b50f.pn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",
    "https://halflife.hackclub-assets.com/hackclub-half-life/sessions/gSMICPeKfFIX4r61sX8jLHHguUkM0Btr/378cd39cac2fd3ea545bb6c8136c01ec41206b467dacadc1b29e9c29417083aa.pn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",
    "https://halflife.hackclub-assets.com/hackclub-half-life/sessions/gSMICPeKfFIX4r61sX8jLHHguUkM0Btr/e187ecc97d25d935846136cca57cd152e7e2bf0f34cf15355a435de18d82b91f.pn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",
    "https://halflife.hackclub-assets.com/hackclub-half-life/sessions/gSMICPeKfFIX4r61sX8jLHHguUkM0Btr/31ce3a0aad3344d69b94c5da8ff59737bd36d12a0cb56e4f1ae70f1bebac14dd.pn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",
    "https://halflife.hackclub-assets.com/hackclub-half-life/sessions/gSMICPeKfFIX4r61sX8jLHHguUkM0Btr/40a35485c4da3ae9c094347a21e765887886bd8506811d5f87424882b952a344.pn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",
    "https://halflife.hackclub-assets.com/hackclub-half-life/sessions/gSMICPeKfFIX4r61sX8jLHHguUkM0Btr/d814b9455769c4e7c8d6c3503dc198a8bcbbfe616ed28c84804c287e9412863d.pn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",
    "https://halflife.hackclub-assets.com/hackclub-half-life/sessions/gSMICPeKfFIX4r61sX8jLHHguUkM0Btr/bc2db1c001d1d81bce4f2f16691ded51a47d57cbce4c1fcb1adfb49931ee5d99.pn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",
    "https://halflife.hackclub-assets.com/hackclub-half-life/sessions/gSMICPeKfFIX4r61sX8jLHHguUkM0Btr/cae16ce9705a4287b5d016bb042c39e04f065694f9e1196ce56d5cf533009ca5.pn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",
    "https://halflife.hackclub-assets.com/hackclub-half-life/sessions/gSMICPeKfFIX4r61sX8jLHHguUkM0Btr/f4fd3f28e1eb4d983b4e0c02e1d72f5e47a18cd43a5570abfe2c30a984876071.pn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",
    "https://halflife.hackclub-assets.com/hackclub-half-life/sessions/gSMICPeKfFIX4r61sX8jLHHguUkM0Btr/83ee80aaa95dd163d5ea2e2f3fed2f73f7b971ac7ab93308adfa669440d1617a.pn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",
    "https://halflife.hackclub-assets.com/hackclub-half-life/sessions/gSMICPeKfFIX4r61sX8jLHHguUkM0Btr/8b0883b320b9a22ea11839199b1c6237220fbd59cfaa9dd3f0a876422835b96f.pn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",
    "https://halflife.hackclub-assets.com/hackclub-half-life/sessions/gSMICPeKfFIX4r61sX8jLHHguUkM0Btr/663c98819a35280e7834c2e614e8f6ecaba066d9b0f043f7295a1e3015651059.pn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"
]

def get_dynamic_ws_url():
    try:
        req = urllib.request.urlopen(CDP_JSON_URL, timeout=5)
        tabs = json.loads(req.read().decode('utf-8'))
        for t in tabs:
            if PROJECT_ID in t.get('url', ''):
                return t.get('webSocketDebuggerUrl'), t.get('url')
    except Exception as e:
        print(f"[WARN] Failed to query dynamic CDP tabs: {e}")
    return None, None

def verify_single_cdn_url(url, retries=2):
    for attempt in range(retries + 1):
        try:
            req = urllib.request.Request(url, headers={'User-Agent': 'Mozilla/5.0'})
            with urllib.request.urlopen(req, timeout=5) as r:
                if r.status == 200:
                    return 200
        except Exception:
            if attempt == retries:
                return "FAIL"
            time.sleep(0.3)
    return "FAIL"

def verify_cdn_images():
    results = {}
    all_ok = True
    for idx, url in enumerate(CDN_IMAGE_URLS):
        res = verify_single_cdn_url(url)
        results[idx] = res
        if res != 200:
            all_ok = False
    return all_ok, results

async def inspect_and_capture(ws_url):
    try:
        async with websockets.connect(ws_url, max_size=50*1024*1024, open_timeout=5) as ws:
            # 1. Evaluate DOM
            cmd = {
                'id': 1,
                'method': 'Runtime.evaluate',
                'params': {
                    'expression': """(() => {
                        const text = document.body.innerText;
                        
                        // Status determinations
                        const isApproved = text.includes('APPROVED') || text.includes('Approved') || text.includes('Design APPROVED');
                        const isInReview = text.includes('IN REVIEW') || text.includes('Design\\nIN REVIEW') || text.includes('waiting for review');
                        const hasSubmitted = text.includes('Submitted. Where it stands with review is below.');
                        const hasUnsubmit = text.includes('UNSUBMIT THIS WARM-UP PROJECT');
                        
                        // Reviewer comments or feedback notes
                        const reviewCards = Array.from(document.querySelectorAll('*')).filter(el => {
                            const t = el.innerText || '';
                            return (t.includes('Reviewer') || t.includes('Feedback') || t.includes('Note from reviewer')) && t.length < 500;
                        }).map(el => el.innerText.trim());
                        
                        // Entries check
                        const e1 = text.includes('Bench Prototyping, Power Budgeting & Dialing In The Hardware');
                        const e2 = text.includes('EasyEDA Schematic Capture, BOM Selection & Layout Planning');
                        const e3 = text.includes('PCB Routing, JLCPCB DRC, Soldering Clearance & Firmware Polish');
                        
                        // Hackatime
                        const hIdx = text.indexOf('HACKATIME');
                        const bIdx = text.indexOf('BILL OF MATERIALS');
                        let ht = '';
                        if (hIdx !== -1 && bIdx !== -1) {
                            ht = text.slice(hIdx, bIdx).trim();
                        }
                        
                        // Total hours logged
                        const hrMatches = text.match(/([0-9.]+)h logged/g) || [];
                        let maxLoggedHour = 0.0;
                        for (const m of hrMatches) {
                            const num = parseFloat(m.replace('h logged', ''));
                            if (!isNaN(num) && num > maxLoggedHour) {
                                maxLoggedHour = num;
                            }
                        }
                        
                        return {
                            url: window.location.href,
                            title: document.title,
                            isApproved,
                            isInReview,
                            hasSubmitted,
                            hasUnsubmit,
                            reviewerNotes: Array.from(new Set(reviewCards)),
                            entries: { e1, e2, e3 },
                            hackatimeSnippet: ht,
                            hoursLogged: hrMatches,
                            maxLoggedHour: maxLoggedHour,
                            hoursSyncedAboveThreshold: maxLoggedHour >= 11.94
                        };
                    })()""",
                    'returnByValue': True
                }
            }
            await ws.send(json.dumps(cmd))
            res = json.loads(await ws.recv())
            portal_val = res.get('result', {}).get('result', {}).get('value', {})
            
            # 2. Capture verification screenshot
            shot_cmd = {
                'id': 2,
                'method': 'Page.captureScreenshot',
                'params': {'format': 'png'}
            }
            await ws.send(json.dumps(shot_cmd))
            shot_res = json.loads(await ws.recv())
            img_b64 = shot_res.get('result', {}).get('data')
            if img_b64:
                with open(SCREENSHOT_FILE, 'wb') as f:
                    f.write(base64.b64decode(img_b64))
            
            return portal_val, True
    except Exception as e:
        return {'error': str(e)}, False

async def sentry_loop(interval_sec=60, max_iterations=None):
    iteration = 0
    print(f"=== STARTING POCKET COMPANION PORTAL SENTRY (Interval: {interval_sec}s) ===")
    
    while True:
        iteration += 1
        now_str = datetime.datetime.now().strftime("%Y-%m-%d %H:%M:%S")
        
        # 1. Dynamically discover active tab ws_url
        ws_url, page_url = get_dynamic_ws_url()
        if not ws_url:
            print(f"[{now_str}][Cycle #{iteration}] WARN: Could not locate tab for project {PROJECT_ID}. Retrying in {interval_sec}s...")
            await asyncio.sleep(interval_sec)
            continue
            
        # 2. Inspect portal state & capture screenshot
        portal_state, shot_saved = await inspect_and_capture(ws_url)
        
        # 3. Verify CDN images with resilient retry
        cdn_ok, cdn_details = verify_cdn_images()
        
        # 4. Check health metrics
        is_approved = portal_state.get('isApproved', False)
        is_submitted = portal_state.get('hasSubmitted', False)
        has_unsubmit = portal_state.get('hasUnsubmit', False)
        is_in_review = portal_state.get('isInReview', False) or is_submitted or has_unsubmit
        hours_ok = portal_state.get('hoursSyncedAboveThreshold', False)
        all_entries_ok = (portal_state.get('entries', {}).get('e1') and 
                          portal_state.get('entries', {}).get('e2') and 
                          portal_state.get('entries', {}).get('e3'))
        
        reviewer_notes = portal_state.get('reviewerNotes', [])
        
        if is_approved:
            current_status = "APPROVED_COMPLETED"
        elif is_in_review and all_entries_ok and cdn_ok and hours_ok:
            current_status = "HEALTHY_SUBMITTED_IN_REVIEW"
        else:
            current_status = "ATTENTION_REQUIRED"
            
        report = {
            "timestamp": now_str,
            "iteration": iteration,
            "status": current_status,
            "ws_url": ws_url,
            "portal": {
                "is_approved": is_approved,
                "is_submitted": is_submitted,
                "has_unsubmit": has_unsubmit,
                "in_review": is_in_review,
                "max_logged_hour": portal_state.get('maxLoggedHour'),
                "hours_logged": portal_state.get('hoursLogged'),
                "hours_synced_above_11_94h": hours_ok,
                "hackatime_project": "pocket-companion (0.57h)"
            },
            "reviewer_notes": reviewer_notes,
            "journal_entries": {
                "entry1_live": portal_state.get('entries', {}).get('e1'),
                "entry2_live": portal_state.get('entries', {}).get('e2'),
                "entry3_live": portal_state.get('entries', {}).get('e3')
            },
            "cdn_images": {
                "verified_all_200": cdn_ok,
                "total_verified": len(CDN_IMAGE_URLS)
            },
            "screenshot_saved": shot_saved,
            "screenshot_path": SCREENSHOT_FILE
        }
        
        # Write heartbeat
        with open(HEARTBEAT_FILE, 'w', encoding='utf-8') as f:
            json.dump(report, f, indent=2)
            
        log_line = f"[{now_str}][Cycle #{iteration}] Status: {report['status']} | Review: {'APPROVED' if is_approved else 'IN REVIEW'} | Notes: {len(reviewer_notes)} | Hours: {portal_state.get('maxLoggedHour')}h (Synced >= 11.94h: {hours_ok}) | Entries (3/3): {all_entries_ok} | CDN (13/13): {cdn_ok} | Screenshot: {shot_saved}\n"
        with open(LOG_FILE, 'a', encoding='utf-8') as f:
            f.write(log_line)
            
        print(log_line.strip())
        sys.stdout.flush()
        
        if max_iterations and iteration >= max_iterations:
            print(f"Reached max iterations ({max_iterations}). Exiting loop.")
            break
            
        await asyncio.sleep(interval_sec)

if __name__ == '__main__':
    max_it = None
    if len(sys.argv) > 1:
        max_it = int(sys.argv[1])
    asyncio.run(sentry_loop(interval_sec=60, max_iterations=max_it))
