partofcosmos-site/pocket-companion/hardware/generate_pcb_3d_isometric_render.py

"""
High-Precision 3D Isometric Board Visualizer for Pocket Companion
Generates: C:\\Users\\white\\pocket-companion\\assets\\journal_media\\08_pcb_3d_render_isometric.png (1920x1080)
"""

import os
import math
import numpy as np
from PIL import Image, ImageDraw, ImageFont, ImageFilter

OUTPUT_PATH = r"C:\Users\white\pocket-companion\assets\journal_media\08_pcb_3d_render_isometric.png"
os.makedirs(os.path.dirname(OUTPUT_PATH), exist_ok=True)

def get_font(size, bold=False, mono=False):
    if mono:
        font_file = "consolab.ttf" if bold else "consola.ttf"
    else:
        font_file = "segoeuib.ttf" if bold else "segoeui.ttf"
    font_path = os.path.join(r"C:\Windows\Fonts", font_file)
    if os.path.exists(font_path):
        return ImageFont.truetype(font_path, size)
    return ImageFont.load_default()

# -----------------------------------------------------------------------------
# 3D CAMERA & PERSPECTIVE PROJECTION
# -----------------------------------------------------------------------------
T = np.array([0.0, 0.0, 2.0])          # Center target (mm)
psi = np.radians(-38.0)                # Yaw
theta = np.radians(31.0)              # Pitch
d = np.array([np.cos(theta)*np.sin(psi), -np.cos(theta)*np.cos(psi), np.sin(theta)])
D = 152.0                             # Distance
C = T + D * d                         # Camera center
f = -d                                # Forward
up = np.array([0.0, 0.0, 1.0])
r = np.cross(f, up)
r = r / np.linalg.norm(r)
u = np.cross(r, f)

F_SCALE = 2850.0                      # Focal scale
U0, V0 = 960.0, 530.0                 # Screen center

def proj(p):
    pc = np.array(p, dtype=float) - C
    xc = float(np.dot(pc, r))
    yc = float(np.dot(pc, u))
    zc = float(np.dot(pc, f))
    if zc <= 0.001:
        zc = 0.001
    return (U0 + F_SCALE * xc / zc, V0 - F_SCALE * yc / zc)

def find_coeffs(pa, pb):
    matrix = []
    for p1, p2 in zip(pa, pb):
        matrix.append([p1[0], p1[1], 1, 0, 0, 0, -p2[0]*p1[0], -p2[0]*p1[1]])
        matrix.append([0, 0, 0, p1[0], p1[1], 1, -p2[1]*p1[0], -p2[1]*p1[1]])
    A = np.matrix(matrix, dtype=float)
    B = np.array(pb).reshape(8)
    res = np.dot(np.linalg.inv(A.T * A) * A.T, B)
    return np.array(res).reshape(8)

# -----------------------------------------------------------------------------
# 1. 2D HIGH-RESOLUTION PCB TOP SURFACE TEXTURE (2600 x 1900 px)
# Mapping: X in [-26, +26] mm -> [0, 2600] px, Y in [+19, -19] mm -> [0, 1900] px
# -----------------------------------------------------------------------------
def mm2px(x, y):
    px = int((x + 26.0) / 52.0 * 2600.0)
    py = int((19.0 - y) / 38.0 * 1900.0)
    return px, py

def create_top_texture():
    tw, th = 2600, 1900
    tex = Image.new("RGBA", (tw, th), (0, 0, 0, 0))
    draw = ImageDraw.Draw(tex)

    cr = 150  # 3.0mm corner radius in px
    # Matte Black Solder Mask Substrate
    draw.rounded_rectangle([(0, 0), (tw - 1, th - 1)], radius=cr, fill=(22, 22, 26, 255))

    # Add realistic micro-texture grain
    np.random.seed(101)
    grain = np.random.randint(-4, 5, (th, tw, 3), dtype=np.int16)
    arr = np.array(tex, dtype=np.int16)
    arr[:, :, :3] = np.clip(arr[:, :, :3] + grain, 0, 255)
    tex = Image.fromarray(np.uint8(arr), "RGBA")
    draw = ImageDraw.Draw(tex)

    # Ground Plane Edge Isolation
    draw.rounded_rectangle([(35, 35), (tw - 36, th - 36)], radius=cr - 25, outline=(30, 30, 38, 255), width=3)

    # 4 Corner M2.5 Mounting Holes (Outer dia 5.0mm = 250px, Drill 2.7mm = 135px)
    mount_coords = [(-23.5, 16.5), (23.5, 16.5), (23.5, -16.5), (-23.5, -16.5)]
    for mx_mm, my_mm in mount_coords:
        mx, my = mm2px(mx_mm, my_mm)
        draw.ellipse([(mx - 140, my - 140), (mx + 140, my + 140)], fill=(16, 16, 20, 255))
        draw.ellipse([(mx - 125, my - 125), (mx + 125, my + 125)], fill=(234, 179, 8, 255), outline=(202, 138, 4, 255), width=4)
        draw.ellipse([(mx - 68, my - 68), (mx + 68, my + 68)], fill=(8, 8, 10, 255), outline=(161, 98, 7, 255), width=3)

    # Ground stitching vias
    via_coords = [
        (-21.0, 5.0), (-21.0, -10.0), (23.5, 5.0), (23.5, -5.0),
        (-10.0, 16.5), (0.0, 16.5), (10.0, 16.5),
        (-18.0, -16.5), (-7.0, -16.5), (7.0, -16.5), (18.0, -16.5),
        (2.0, -5.0), (14.0, -5.0)
    ]
    for vx_mm, vy_mm in via_coords:
        vx, vy = mm2px(vx_mm, vy_mm)
        draw.ellipse([(vx - 28, vy - 28), (vx + 28, vy + 28)], fill=(234, 179, 8, 255), outline=(202, 138, 4, 255), width=2)
        draw.ellipse([(vx - 12, vy - 12), (vx + 12, vy + 12)], fill=(8, 8, 10, 255))

    # Copper Traces Underneath Solder Mask
    trace_col = (36, 38, 48, 255)
    trace_hi = (48, 52, 66, 255)
    def trace(mm_pts, w=16):
        pts = [mm2px(x, y) for x, y in mm_pts]
        draw.line(pts, fill=trace_hi, width=w + 6)
        draw.line(pts, fill=trace_col, width=w)

    trace([(-8.0, 4.0), (-3.0, 4.0), (2.0, 9.0), (7.0, 9.0)], w=14)   # SDA to OLED
    trace([(-8.0, 2.0), (-2.0, 2.0), (3.0, 7.0), (9.0, 7.0)], w=14)   # SCL to OLED
    trace([(-8.0, -2.0), (-8.0, -8.0), (-13.0, -8.0), (-13.0, -11.0)], w=14) # GP2 to Left Button
    trace([(-6.0, -4.0), (-6.0, -8.0), (0.0, -8.0), (0.0, -11.0)], w=14)       # GP3 to Action Button
    trace([(-4.0, -4.0), (-4.0, -7.0), (13.0, -7.0), (13.0, -11.0)], w=14)     # GP4 to Right Button
    trace([(-1.0, 0.0), (5.0, 0.0), (14.0, -2.0), (18.0, -2.0)], w=14)         # GP5 to Buzzer
    trace([(-20.0, 11.0), (-23.0, 11.0), (-23.0, -2.0)], w=28)                 # VBAT from JST to Switch
    trace([(-22.0, -5.0), (-15.0, -5.0), (-15.0, 0.0), (-12.0, 0.0)], w=28)   # Switched power to RP2040

    # Gold ENIG Pads
    gold_fill = (245, 158, 11, 255)
    gold_edge = (180, 83, 9, 255)
    gold_hi = (253, 224, 71, 255)
    def pad_mm(x0, y0, x1, y1, r=8):
        px0, py1 = mm2px(x0, y0)
        px1, py0 = mm2px(x1, y1)
        if px0 > px1: px0, px1 = px1, px0
        if py0 > py1: py0, py1 = py1, py0
        draw.rounded_rectangle([(px0 - 8, py0 - 8), (px1 + 8, py1 + 8)], radius=r + 4, fill=(14, 14, 18, 255))
        draw.rounded_rectangle([(px0, py0), (px1, py1)], radius=r, fill=gold_fill, outline=gold_edge, width=2)
        draw.line([(px0 + 4, py0 + 3), (px1 - 4, py0 + 3)], fill=gold_hi, width=2)

    # RP2040-Zero Solder Pads
    for i in range(9):
        py = -4.0 + i * 2.3
        pad_mm(-17.8, py - 0.4, -16.2, py + 0.4, r=4)
        pad_mm(0.2, py - 0.4, 1.8, py + 0.4, r=4)
    for i in range(5):
        px = -14.0 + i * 3.0
        pad_mm(px - 0.4, -6.5, px + 0.4, -5.0, r=4)

    # OLED 4-Pin Female Header Pads (X = 4.0 to 14.5, Y = 12.0)
    for px in [5.5, 8.5, 11.5, 14.5]:
        pad_mm(px - 0.7, 11.3, px + 0.7, 12.7, r=8)
        cx, cy = mm2px(px, 12.0)
        draw.ellipse([(cx - 14, cy - 14), (cx + 14, cy + 14)], fill=(8, 8, 10, 255))

    # 3x Tactile Push Button Footprints (X = -13, 0, +13, Y = -12)
    for bx in [-13.0, 0.0, 13.0]:
        pad_mm(bx - 3.8, -13.5, bx - 2.6, -12.5, r=4)
        pad_mm(bx + 2.6, -13.5, bx + 3.8, -12.5, r=4)
        pad_mm(bx - 3.8, -11.5, bx - 2.6, -10.5, r=4)
        pad_mm(bx + 2.6, -11.5, bx + 3.8, -10.5, r=4)

    # Slide Switch Footprint
    for sy in [-5.5, -4.0, -2.5]:
        pad_mm(-24.5, sy - 0.4, -22.5, sy + 0.4, r=4)
    pad_mm(-24.2, -6.8, -22.8, -6.0, r=4)
    pad_mm(-24.2, -2.0, -22.8, -1.2, r=4)
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
